naco-design/Generalized_CAD/Keycaps/Flat/2U-H.stp

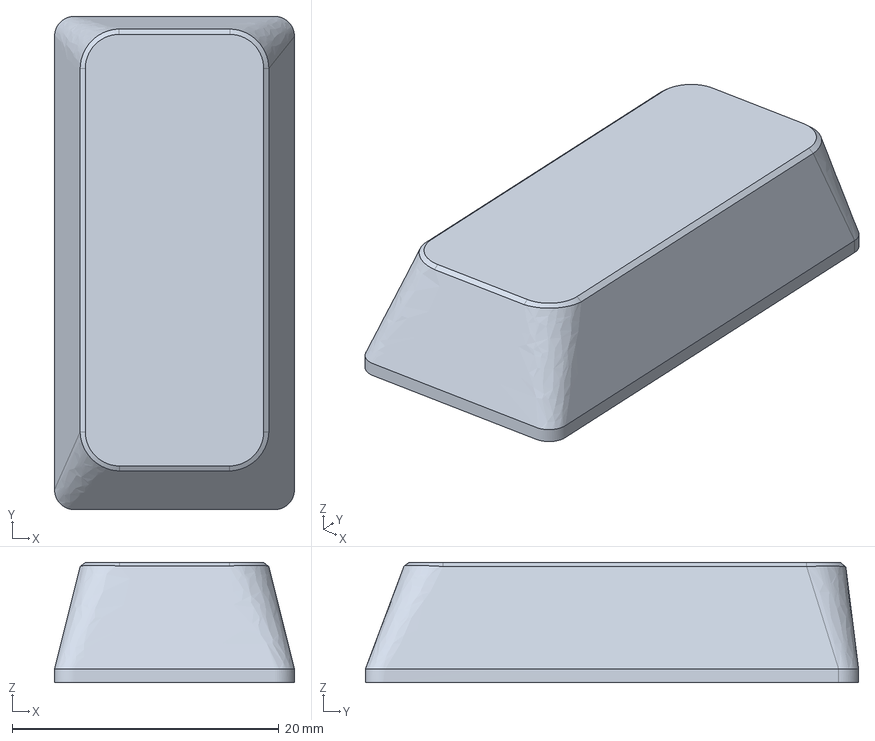
[picture p17: CAD file, 2025-01-10]
Keycaps/Flat/2U-H.stp
18.0 x 37.0 x 9.00 mm
