naco-design/Generalized_CAD/Keycaps/Flat/cap_Ent.stp

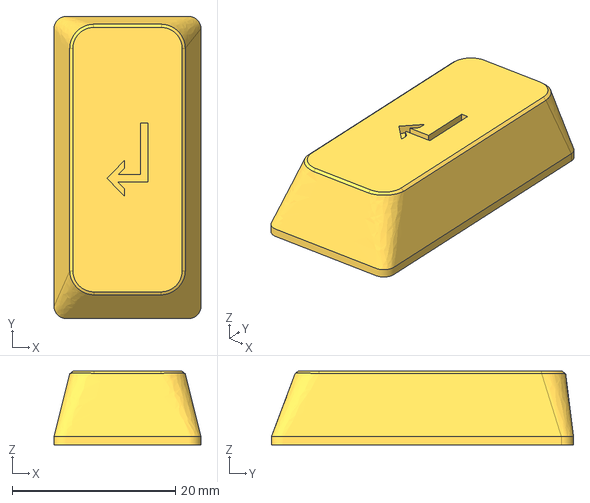
[picture p18: CAD file, 2025-01-10]
Keycaps/Flat/cap_Ent.stp
18.0 x 37.0 x 9.00 mm
